MyFreertosLab/sdrone_test/main/sdrone_motors_task.c

/*
 * sdrone_motors_task.c
 *
 *  Created on: 19 apr 2021
 *      Author: andrea
 */
#include <stdio.h>
#include <stdlib.h>
#include <string.h>
#include <math.h>
#include <freertos/FreeRTOS.h>
#include <freertos/task.h>
#include <esp_system.h>
#include <motors.h>
#include <sdrone_motors_task.h>
#include <driver/i2c.h>
#include <ina3221.h>


void sdrone_motors_controller_init(
		sdrone_motors_state_handle_t sdrone_motors_state_handle) {
	printf("sdrone_motors_controller_init init initial state and motors\n");
	memset(sdrone_motors_state_handle, 0, sizeof(*sdrone_motors_state_handle));
	ESP_ERROR_CHECK(motors_init(&(sdrone_motors_state_handle->motors)));

	sdrone_motors_state_handle->motors_task_handle =
			xTaskGetCurrentTaskHandle();

	// voltage & current sensor (3 channels);
	printf("sdrone_motors_controller_init init ina3221 sensor\n");
//	static ina3221_t ina3221;
//	ina3221_handle_t ina3221_handle = &ina3221;
//	ina3221_handle->i2c_master_port = MOTORS_INA3221_I2C_PORT;
//	ESP_ERROR_CHECK(ina3221_init(ina3221_handle));
//	ESP_ERROR_CHECK(ina3221_test_connection(ina3221_handle));
//	sdrone_motors_state_handle->ina3221_handle = ina3221_handle;
	printf("sdrone_motors_controller_init initial state and motors initialized\n");
}

void sdrone_motors_controller_cycle(
		sdrone_motors_state_handle_t sdrone_motors_state_handle) {
	motors_handle_t motors_handle = &(sdrone_motors_state_handle->motors);

	printf("sdrone_motors_task_init::Arm motors\n");
	ESP_ERROR_CHECK(motors_arm(motors_handle));
	vTaskDelay(pdMS_TO_TICKS(10));

	while (true) {
		// Take Notify at end of duty_cycle
		if (ulTaskNotifyTake( pdTRUE, pdMS_TO_TICKS(10))
				== sdrone_motors_state_handle->controller_driver_id) {
			if (sdrone_motors_state_handle->input.isCommand) {
				switch (sdrone_motors_state_handle->input.command.type) {
				case MOTORS_ARM: {
					ESP_ERROR_CHECK(motors_arm(motors_handle));
					break;
				}
				case MOTORS_DISARM: {
					ESP_ERROR_CHECK(motors_disarm(motors_handle));
					break;
				}
				case MOTORS_SWITCHOFF: {
					ESP_ERROR_CHECK(motors_switchoff(motors_handle));
					break;
				}
				case MOTORS_SWITCHON: {
					ESP_ERROR_CHECK(motors_switchon(motors_handle));
					break;
				}
				default: {
					printf(
							"ERROR: sdrone_motors_controller_cycle::command %d unknown for motors",
							sdrone_motors_state_handle->input.command.type);
				}
				}
			} else if (sdrone_motors_state_handle->input.data.tx_rx_flag
					== MOTORS_TXRX_TRANSMITTED) {
#ifdef MOTORS_FRAME_HORIZONTAL_HEXACOPTER
				// TODO: T.B.D.
#else
#ifdef MOTORS_FRAME_TWO_HORIZONTAL_AXIS
				ESP_ERROR_CHECK(motors_newton_to_duty(sdrone_motors_state_handle->input.data.thrust[0], &motors_handle->motor[0].duty_cycle));
				ESP_ERROR_CHECK(motors_newton_to_duty(sdrone_motors_state_handle->input.data.thrust[1], &motors_handle->motor[1].duty_cycle));
#endif
#endif
//				ESP_ERROR_CHECK(ina3321_load_data(sdrone_motors_state_handle->ina3221_handle));
//				printf("%2.3f, %2.3f, %d, %d, %d, %d, %d, %d;\n",
//						sdrone_motors_state_handle->input.data.thrust,
//						duty_prev,
//						sdrone_motors_state_handle->ina3221_handle->raw_data.channel_data[0].bus_voltage,
//						sdrone_motors_state_handle->ina3221_handle->raw_data.channel_data[0].shunt_voltage,
//						sdrone_motors_state_handle->ina3221_handle->raw_data.channel_data[1].bus_voltage,
//						sdrone_motors_state_handle->ina3221_handle->raw_data.channel_data[1].shunt_voltage,
//						sdrone_motors_state_handle->ina3221_handle->raw_data.channel_data[2].bus_voltage,
//						sdrone_motors_state_handle->ina3221_handle->raw_data.channel_data[2].shunt_voltage
//					  );

				ESP_ERROR_CHECK(motors_update(motors_handle));
				sdrone_motors_state_handle->input.data.tx_rx_flag =
						MOTORS_TXRX_RECEIVED;
			}
		}
	}
}

void sdrone_motors_task(void *arg) {
	sdrone_motors_state_handle_t sdrone_motors_state_handle =
			(sdrone_motors_state_handle_t) arg;
	sdrone_motors_controller_init(sdrone_motors_state_handle);
	sdrone_motors_controller_cycle(sdrone_motors_state_handle);

}
