MyFreertosLab/sdrone_test/components/drivers/mpu9250/include/mpu9250.h

#ifndef _MPU9250_H_
#define _MPU9250_H_

#include <esp_err.h>
#include <driver/spi_master.h>
#include "freertos/task.h"

#define MPU9250_ID 0x70
#define X_POS 0
#define Y_POS 1
#define Z_POS 2

enum mpu9250_register {
	MPU9250_SELF_TEST_X_GYRO =  0x00,
	MPU9250_SELF_TEST_Y_GYRO =  0x01,
	MPU9250_SELF_TEST_Z_GYRO =  0x02,
	MPU9250_SELF_TEST_X_ACCEL = 0x0D,
	MPU9250_SELF_TEST_Y_ACCEL = 0x0E,
	MPU9250_SELF_TEST_Z_ACCEL = 0x0F,
	MPU9250_XG_OFFSET_H =       0x13,
	MPU9250_XG_OFFSET_L =       0x14,
	MPU9250_YG_OFFSET_H =       0x15,
	MPU9250_YG_OFFSET_L =       0x16,
	MPU9250_ZG_OFFSET_H =       0x17,
	MPU9250_ZG_OFFSET_L =       0x18,
	MPU9250_SMPLRT_DIV =        0x19,
	MPU9250_CONFIG =            0x1A,
	MPU9250_GYRO_CONFIG =       0x1B,
	MPU9250_ACCEL_CONFIG =      0x1C,
	MPU9250_ACCEL_CONFIG_2 =    0x1D,
	MPU9250_LP_ACCEL_ODR =      0x1E,
	MPU9250_WOM_THR =           0x1F,
	MPU9250_FIFO_EN =           0x23,
	MPU9250_I2C_MST_CTRL =      0x24,
	MPU9250_I2C_SLV0_ADDR =     0x25,
	MPU9250_I2C_SLV0_REG =      0x26,
	MPU9250_I2C_SLV0_CTRL =     0x27,
	MPU9250_I2C_SLV1_ADDR =     0x28,
	MPU9250_I2C_SLV1_REG =      0x29,
	MPU9250_I2C_SLV1_CTRL =     0x2A,
	MPU9250_I2C_SLV2_ADDR =     0x2B,
	MPU9250_I2C_SLV2_REG =      0x2C,
	MPU9250_I2C_SLV2_CTRL =     0x2D,
	MPU9250_I2C_SLV3_ADDR =     0x2E,
	MPU9250_I2C_SLV3_REG =      0x2F,
	MPU9250_I2C_SLV3_CTRL =     0x30,
	MPU9250_I2C_SLV4_ADDR =     0x31,
	MPU9250_I2C_SLV4_REG =      0x32,
	MPU9250_I2C_SLV4_DO =       0x33,
	MPU9250_I2C_SLV4_CTRL =     0x34,
	MPU9250_I2C_SLV4_DI =       0x35,
	MPU9250_I2C_MST_STATUS =    0x36,
	MPU9250_INT_PIN_CFG =       0x37,
	MPU9250_INT_ENABLE =        0x38,
	MPU9250_INT_STATUS =        0x3A,
	MPU9250_ACCEL_XOUT_H =      0x3B,
	MPU9250_ACCEL_XOUT_L =      0x3C,
	MPU9250_ACCEL_YOUT_H =      0x3D,
	MPU9250_ACCEL_YOUT_L =      0x3E,
	MPU9250_ACCEL_ZOUT_H =      0x3F,
	MPU9250_ACCEL_ZOUT_L =      0x40,
	MPU9250_TEMP_OUT_H =        0x41,
	MPU9250_TEMP_OUT_L =        0x42,
	MPU9250_GYRO_XOUT_H =       0x43,
	MPU9250_GYRO_XOUT_L =       0x44,
	MPU9250_GYRO_YOUT_H =       0x45,
	MPU9250_GYRO_YOUT_L =       0x46,
	MPU9250_GYRO_ZOUT_H =       0x47,
	MPU9250_GYRO_ZOUT_L =       0x48,
	MPU9250_EXT_SENS_DATA_00 =  0x49,
	MPU9250_EXT_SENS_DATA_01 =  0x4A,
	MPU9250_EXT_SENS_DATA_02 =  0x4B,
	MPU9250_EXT_SENS_DATA_03 =  0x4C,
	MPU9250_EXT_SENS_DATA_04 =  0x4D,
	MPU9250_EXT_SENS_DATA_05 =  0x4E,
	MPU9250_EXT_SENS_DATA_06 =  0x4F,
	MPU9250_EXT_SENS_DATA_07 =  0x50,
	MPU9250_EXT_SENS_DATA_08 =  0x51,
	MPU9250_EXT_SENS_DATA_09 =  0x52,
	MPU9250_EXT_SENS_DATA_10 =  0x53,
	MPU9250_EXT_SENS_DATA_11 =  0x54,
	MPU9250_EXT_SENS_DATA_12 =  0x55,
	MPU9250_EXT_SENS_DATA_13 =  0x56,
	MPU9250_EXT_SENS_DATA_14 =  0x57,
	MPU9250_EXT_SENS_DATA_15 =  0x58,
	MPU9250_EXT_SENS_DATA_16 =  0x59,
	MPU9250_EXT_SENS_DATA_17 =  0x5A,
	MPU9250_EXT_SENS_DATA_18 =  0x5B,
	MPU9250_EXT_SENS_DATA_19 =  0x5C,
	MPU9250_EXT_SENS_DATA_20 =  0x5D,
	MPU9250_EXT_SENS_DATA_21 =  0x5E,
	MPU9250_EXT_SENS_DATA_22 =  0x5F,
	MPU9250_EXT_SENS_DATA_23 =  0x60,
	MPU9250_I2C_SLV0_DO =       0x63,
	MPU9250_I2C_SLV1_DO =       0x64,
	MPU9250_I2C_SLV2_DO =       0x65,
	MPU9250_I2C_SLV3_DO =       0x66,
	MPU9250_I2C_MST_DELAY_CTRL =0x67,
	MPU9250_SIGNAL_PATH_RESET = 0x68,
	MPU9250_MOT_DETECT_CTRL =   0x69,
	MPU9250_USER_CTRL =         0x6A,
	MPU9250_PWR_MGMT_1 =        0x6B,
	MPU9250_PWR_MGMT_2 =        0x6C,
	MPU9250_FIFO_COUNTH =       0x72,
	MPU9250_FIFO_COUNTL =       0x73,
	MPU9250_FIFO_R_W =          0x74,
	MPU9250_WHO_AM_I =          0x75,
	MPU9250_XA_OFFSET_H =       0x77,
	MPU9250_XA_OFFSET_L =       0x78,
	MPU9250_YA_OFFSET_H =       0x7A,
	MPU9250_YA_OFFSET_L =       0x7B,
	MPU9250_ZA_OFFSET_H =       0x7D,
	MPU9250_ZA_OFFSET_L =       0x7E
};
#define MPU9250_WHO_AM_I_RESULT 0x70

/*********************************
*********** Gyroscope ************
*********************************/
enum gyro_config_bits {
	GYRO_CONFIG_FCHOICE_B = 0,
	GYRO_CONFIG_GYRO_FS_SEL = 3,
	GYRO_CONFIG_ZGYRO_CTEN = 5,
	GYRO_CONFIG_YGYRO_CTEN = 6,
	GYRO_CONFIG_XGYRO_CTEN = 7,
};

/* Gyro Full scale ranges. */
enum gyro_fsr_e {
    INV_FSR_250DPS = 0,
    INV_FSR_500DPS,
    INV_FSR_1000DPS,
    INV_FSR_2000DPS,
    NUM_GYRO_FSR
};

#define MPU9250_GYRO_FSR_MASK     0xE7
#define MPU9250_GYRO_FSR_LBIT     0x03
#define MPU9250_GYRO_FCHOICE_MASK 0x03

/*********************************
********* Accelerometer **********
*********************************/
enum accel_config_bit {
	ACCEL_CONFIG_ACCEL_FS_SEL = 3,
	ACCEL_CONFIG_AZ_ST_EN = 5,
	ACCEL_CONFIG_AY_ST_EN = 6,
	ACCEL_CONFIG_AX_ST_EN = 7,
};
#define MPU9250_ACC_FSR_MASK    0xE7
#define MPU9250_ACC_FSR_LBIT    0x03


enum accel_config_2_bits {
	ACCEL_CONFIG_2_A_DLPFCFG = 0,
	ACCEL_CONFIG_2_ACCEL_FCHOICE_B = 3,
};

/* Accel Full scale ranges. */
enum accel_fsr_e {
    INV_FSR_2G = 0,
    INV_FSR_4G,
    INV_FSR_8G,
    INV_FSR_16G,
    NUM_ACCEL_FSR
};
/* Low-power accel wakeup rates. */
enum lp_accel_rate_e {
    INV_LPA_0_3125HZ,
    INV_LPA_0_625HZ,
    INV_LPA_1_25HZ,
    INV_LPA_2_5HZ,
    INV_LPA_5HZ,
    INV_LPA_10HZ,
    INV_LPA_20HZ,
    INV_LPA_40HZ,
    INV_LPA_80HZ,
    INV_LPA_160HZ,
    INV_LPA_320HZ,
    INV_LPA_640HZ
};

/*********************************
******* Power Management *********
*********************************/
enum pwr_mgmt_1_bits {
	PWR_MGMT_1_CLKSEL = 0,
	PWR_MGMT_1_PD_PTAT = 3,
	PWR_MGMT_1_GYRO_STANDBY = 4,
	PWR_MGMT_1_CYCLE = 5,
	PWR_MGMT_1_SLEEP = 6,
	PWR_MGMT_1_H_RESET = 7
};

enum pwr_mgmt_2_bits {
	PWR_MGMT_2_DISABLE_ZG = 0,
	PWR_MGMT_2_DISABLE_YG = 1,
	PWR_MGMT_2_DISABLE_XG = 2,
	PWR_MGMT_2_DISABLE_ZA = 3,
	PWR_MGMT_2_DISABLE_YA = 4,
	PWR_MGMT_2_DISABLE_XA = 5,
};

/*********************************
*********** Interrupts ***********
*********************************/
enum interrupt_status_bits {
	INT_STATUS_RAW_DATA_RDY_INT = 0,
	INT_STATUS_RAW_DMP_INT = 1,
	INT_STATUS_FSYNC_INT = 3,
	INT_STATUS_FIFO_OVERFLOW_INT = 4,
	INT_STATUS_WOM_INT = 6,
};

enum int_enable_bits {
	INT_ENABLE_RAW_RDY_EN = 0,
	INT_ENABLE_FSYNC_INT_EN = 3,
	INT_ENABLE_FIFO_OVERFLOW_EN = 4,
	INT_ENABLE_WOM_EN = 6,
};

enum int_pin_cfg_bits {
	INT_PIN_CFG_BYPASS_EN = 1,
	INT_PIN_CFG_FSYNC_INT_MODE_EN = 2,
	INT_PIN_CFG_ACTL_FSYNC = 3,
	INT_PIN_CFG_INT_ANYRD_2CLEAR = 4,
	INT_PIN_CFG_LATCH_INT_EN = 5,
	INT_PIN_CFG_OPEN = 6,
	INT_PIN_CFG_ACTL = 7,
};
#define INT_PIN_CFG_INT_MASK 0xF0

/*********************************
************* Compass ************
*********************************/
enum ak8963_register {
	AK8963_WIA = 0x0,
	AK8963_INFO = 0x1,
	AK8963_ST1 = 0x2,
	AK8963_HXL = 0x3,
	AK8963_HXH = 0x4,
	AK8963_HYL = 0x5,
	AK8963_HYH = 0x6,
	AK8963_HZL = 0x7,
	AK8963_HZH = 0x8,
	AK8963_ST2 = 0x9,
	AK8963_CNTL1 = 0xA,
	AK8963_CNTL2 = 0xB,
	AK8963_ASTC = 0xC,
	AK8963_TS1 = 0xD,
	AK8963_TS2 = 0xE,
	AK8963_I2CDIS = 0xF,
	AK8963_ASAX = 0x10,
	AK8963_ASAY = 0x11,
	AK8963_ASAZ = 0x12,
	AK8963_RSV = 0x13
};

#define MAG_CTRL_OP_MODE_MASK 0xF
#define AK8963_ST1_DRDY_BIT 0
#define AK8963_WHO_AM_I_RESULT 0x48
#define AK8963_ADDRESS 0x0C

/*********************************
********* Low Pass Filter ********
*********************************/
enum lpf_e {
    INV_FILTER_256HZ_NOLPF2 = 0,
    INV_FILTER_188HZ,
    INV_FILTER_98HZ,
    INV_FILTER_42HZ,
    INV_FILTER_20HZ,
    INV_FILTER_10HZ,
    INV_FILTER_5HZ,
    INV_FILTER_2100HZ_NOLPF,
    NUM_FILTER
};


/*********************************
********* Clock Sources **********
*********************************/
enum clock_sel_e {
    INV_CLK_INTERNAL = 0,
    INV_CLK_PLL,
    NUM_CLK
};
/*********************************
*********** Utilities ************
*********************************/
typedef union {
   int16_t array[3];
   struct {
     int16_t x;
     int16_t y;
     int16_t z;
   } xyz;
} mpu9250_int_3d_t;

typedef union {
   int32_t array[3];
   struct {
     int32_t x;
     int32_t y;
     int32_t z;
   } xyz;
} mpu9250_int32_3d_t;

typedef union {
   int64_t array[3];
   struct {
     int64_t x;
     int64_t y;
     int64_t z;
   } xyz;
} mpu9250_int64_3d_t;

typedef union {
   uint16_t array[3];
   struct {
     uint16_t x;
     uint16_t y;
     uint16_t z;
   } xyz;
} mpu9250_uint_3d_t;

typedef union {
   uint32_t array[3];
   struct {
     uint32_t x;
     uint32_t y;
     uint32_t z;
   } xyz;
} mpu9250_uint32_3d_t;

typedef union {
   uint64_t array[3];
   struct {
     uint64_t x;
     uint64_t y;
     uint64_t z;
   } xyz;
} mpu9250_uint64_3d_t;

typedef union {
   double array[3];
   struct {
     double x;
     double y;
     double z;
   } xyz;
} mpu9250_double_3d_t;

/* Se necessario usare
 * float fixed point
 * 22bit integer, 10bit decimal
 * precision: 1/(2^10-1) = 0,000977517
 *
 *
 */

/*
 * we assume this cycle:
 * Calc Predition:
 *   X(k)=A*X(k-1)+B*u(k-1)
 *   P(k)=A*P(k-1)*A'+Q
 * Calc Update:
 *   K(k)=P(k)H'(H*P(k)*H'+R)^(-1)
 *   X(k)=X(k)-K(k)(Sample(k)-H*X(k))
 *   P(k)=(I-K(k)*H)*P(k)
 * with:
 *   A=H=1,
 *   B=Q=0,
 *   R=variance of state,
 * then:
 *   initialization:
 *     X(0)=fixed expected response
 *     P(0)=1
 *     Q=1.5
 *   cycle for each sample
 *     X(k)=X(k-1)
 *     P(k)=P(k-1)+Q
 *     K(k)=P(k)/(P(k)+R)
 *     X(k)=X(k)+K(k)*(Sample(k)-X(k))
 *     P(k)=(1-K(k))*P(k)
 */
typedef struct {
	int16_t X,sample;
	uint16_t R;
	float P,Q,K;
} mpu9250_kalman_t;

/* Offsets */
typedef mpu9250_int_3d_t mpu9250_offset_t;
typedef mpu9250_offset_t* mpu9250_offset_buff_t;

/* Media */
typedef mpu9250_int_3d_t mpu9250_means_t;
typedef mpu9250_means_t* mpu9250_means_buff_t;

/* Varianza */
typedef mpu9250_uint_3d_t mpu9250_var_t;
typedef mpu9250_var_t* mpu9250_var_buff_t;

/* Scarto quadratico medio */
typedef mpu9250_int_3d_t mpu9250_sqm_t;
typedef mpu9250_sqm_t* mpu9250_sqm_buff_t;

/* RPY */
typedef mpu9250_double_3d_t mpu9250_rpy_t;

typedef struct {
    mpu9250_offset_t offset;
    mpu9250_means_t means[4];
    mpu9250_var_t var[4];
    mpu9250_sqm_t sqm[4];
    mpu9250_kalman_t kalman[3];
} mpu9250_cal_data_t;

/* Circular Buffer */
#define CIRCULAR_BUFFER_SIZE 5
typedef struct {
	int16_t data[CIRCULAR_BUFFER_SIZE];
	uint8_t cursor;
} mpu9250_cb_t;
typedef mpu9250_cb_t* mpu9250_cb_handle_t;

#define PI_2 6.283185307f
#define PI 3.141592654f
#define PI_HALF 1.570796327f

/********************************************************************************************************************
********** MPU9250 API **********************************************************************************************
********************************************************************************************************************/
typedef union {
   struct {
     int16_t accel[3];
     int16_t temp;
     int16_t gyro[3];
     int16_t ext[12];
   } data_s_vector;
   struct {
     int16_t accel_data_x;
     int16_t accel_data_y;
     int16_t accel_data_z;
     int16_t temp_data;
     int16_t gyro_data_x;
     int16_t gyro_data_y;
     int16_t gyro_data_z;
     int16_t ext_data[12];
   } data_s_xyz;
} mpu9250_raw_data_t;
typedef mpu9250_raw_data_t* mpu9250_raw_data_buff_t;

/*********************************
********* ACCELEROMETER **********
*********************************/
typedef struct mpu9250_accel_s {
    mpu9250_cal_data_t cal; // calibration data
	uint8_t fsr;
    uint16_t lsb;
	mpu9250_cb_t cb[3]; // circular buffer
	mpu9250_rpy_t rpy;
} mpu9250_accel_t;

/*********************************
*********** GYROSCOPE ************
*********************************/
typedef struct mpu9250_gyro_s {
    mpu9250_cal_data_t cal; // calibration data
	uint8_t fsr;
    float lsb;
	mpu9250_cb_t cb[3]; // circular buffer
	mpu9250_rpy_t rpy;
	mpu9250_cb_t cb_alfa[3]; // circular buffer for alfa
	float alfa[3];
} mpu9250_gyro_t;

typedef uint8_t mpu9250_int_status_t;

/*********************************
******** MPU9250 HANDLE **********
*********************************/
typedef enum {
        IMU_TXRX_IGNORE = 0,
        IMU_TXRX_TRANSMITTED = 1,
        IMU_TXRX_RECEIVED = 2
} imu_txrx_signal_t;
typedef struct {
    mpu9250_raw_data_t raw_data;
    mpu9250_accel_t accel;
    mpu9250_gyro_t gyro;
	double attitude[3];
	volatile imu_txrx_signal_t txrx_signal;
} mpu9250_data_t;

typedef struct mpu9250_init_s {
	spi_bus_config_t buscfg;
	spi_device_interface_config_t devcfg;
	spi_device_handle_t device_handle;
	TaskHandle_t data_ready_task_handle;

	// int config and status
	int int_pin;
    uint8_t int_status;

    // MPU9250 id
    uint8_t whoami;
    mpu9250_data_t data;
    uint16_t data_rate;
} mpu9250_init_t;

typedef mpu9250_init_t* mpu9250_handle_t;

#define MPU9250_READ_FLAG 0x80

/* Private Methods */
void mpu9250_cb_add(mpu9250_cb_handle_t cb, int16_t val);
void mpu9250_cb_means(mpu9250_cb_handle_t cb, int16_t* mean);
void mpu9250_cb_last(mpu9250_cb_handle_t cb, int16_t* val);

/* Public Methids */
/* Set up APIs */
esp_err_t mpu9250_init(mpu9250_handle_t mpu9250_handle);
esp_err_t mpu9250_test_connection(mpu9250_handle_t mpu9250_handle);
esp_err_t mpu9250_load_whoami(mpu9250_handle_t mpu9250_handle);
esp_err_t mpu9250_load_int_status(mpu9250_handle_t mpu9250_handle);
esp_err_t mpu9250_load_raw_data(mpu9250_handle_t mpu9250_handle);
esp_err_t mpu9250_load_data(mpu9250_handle_t mpu9250_handle);

#endif // _MPU9250_H_
